copsvsninjas/Wicked/WickedBoard/WickedBoard.kicad_sch

## KiCad design WickedBoard/WickedBoard.kicad_sch (2024-12-09)

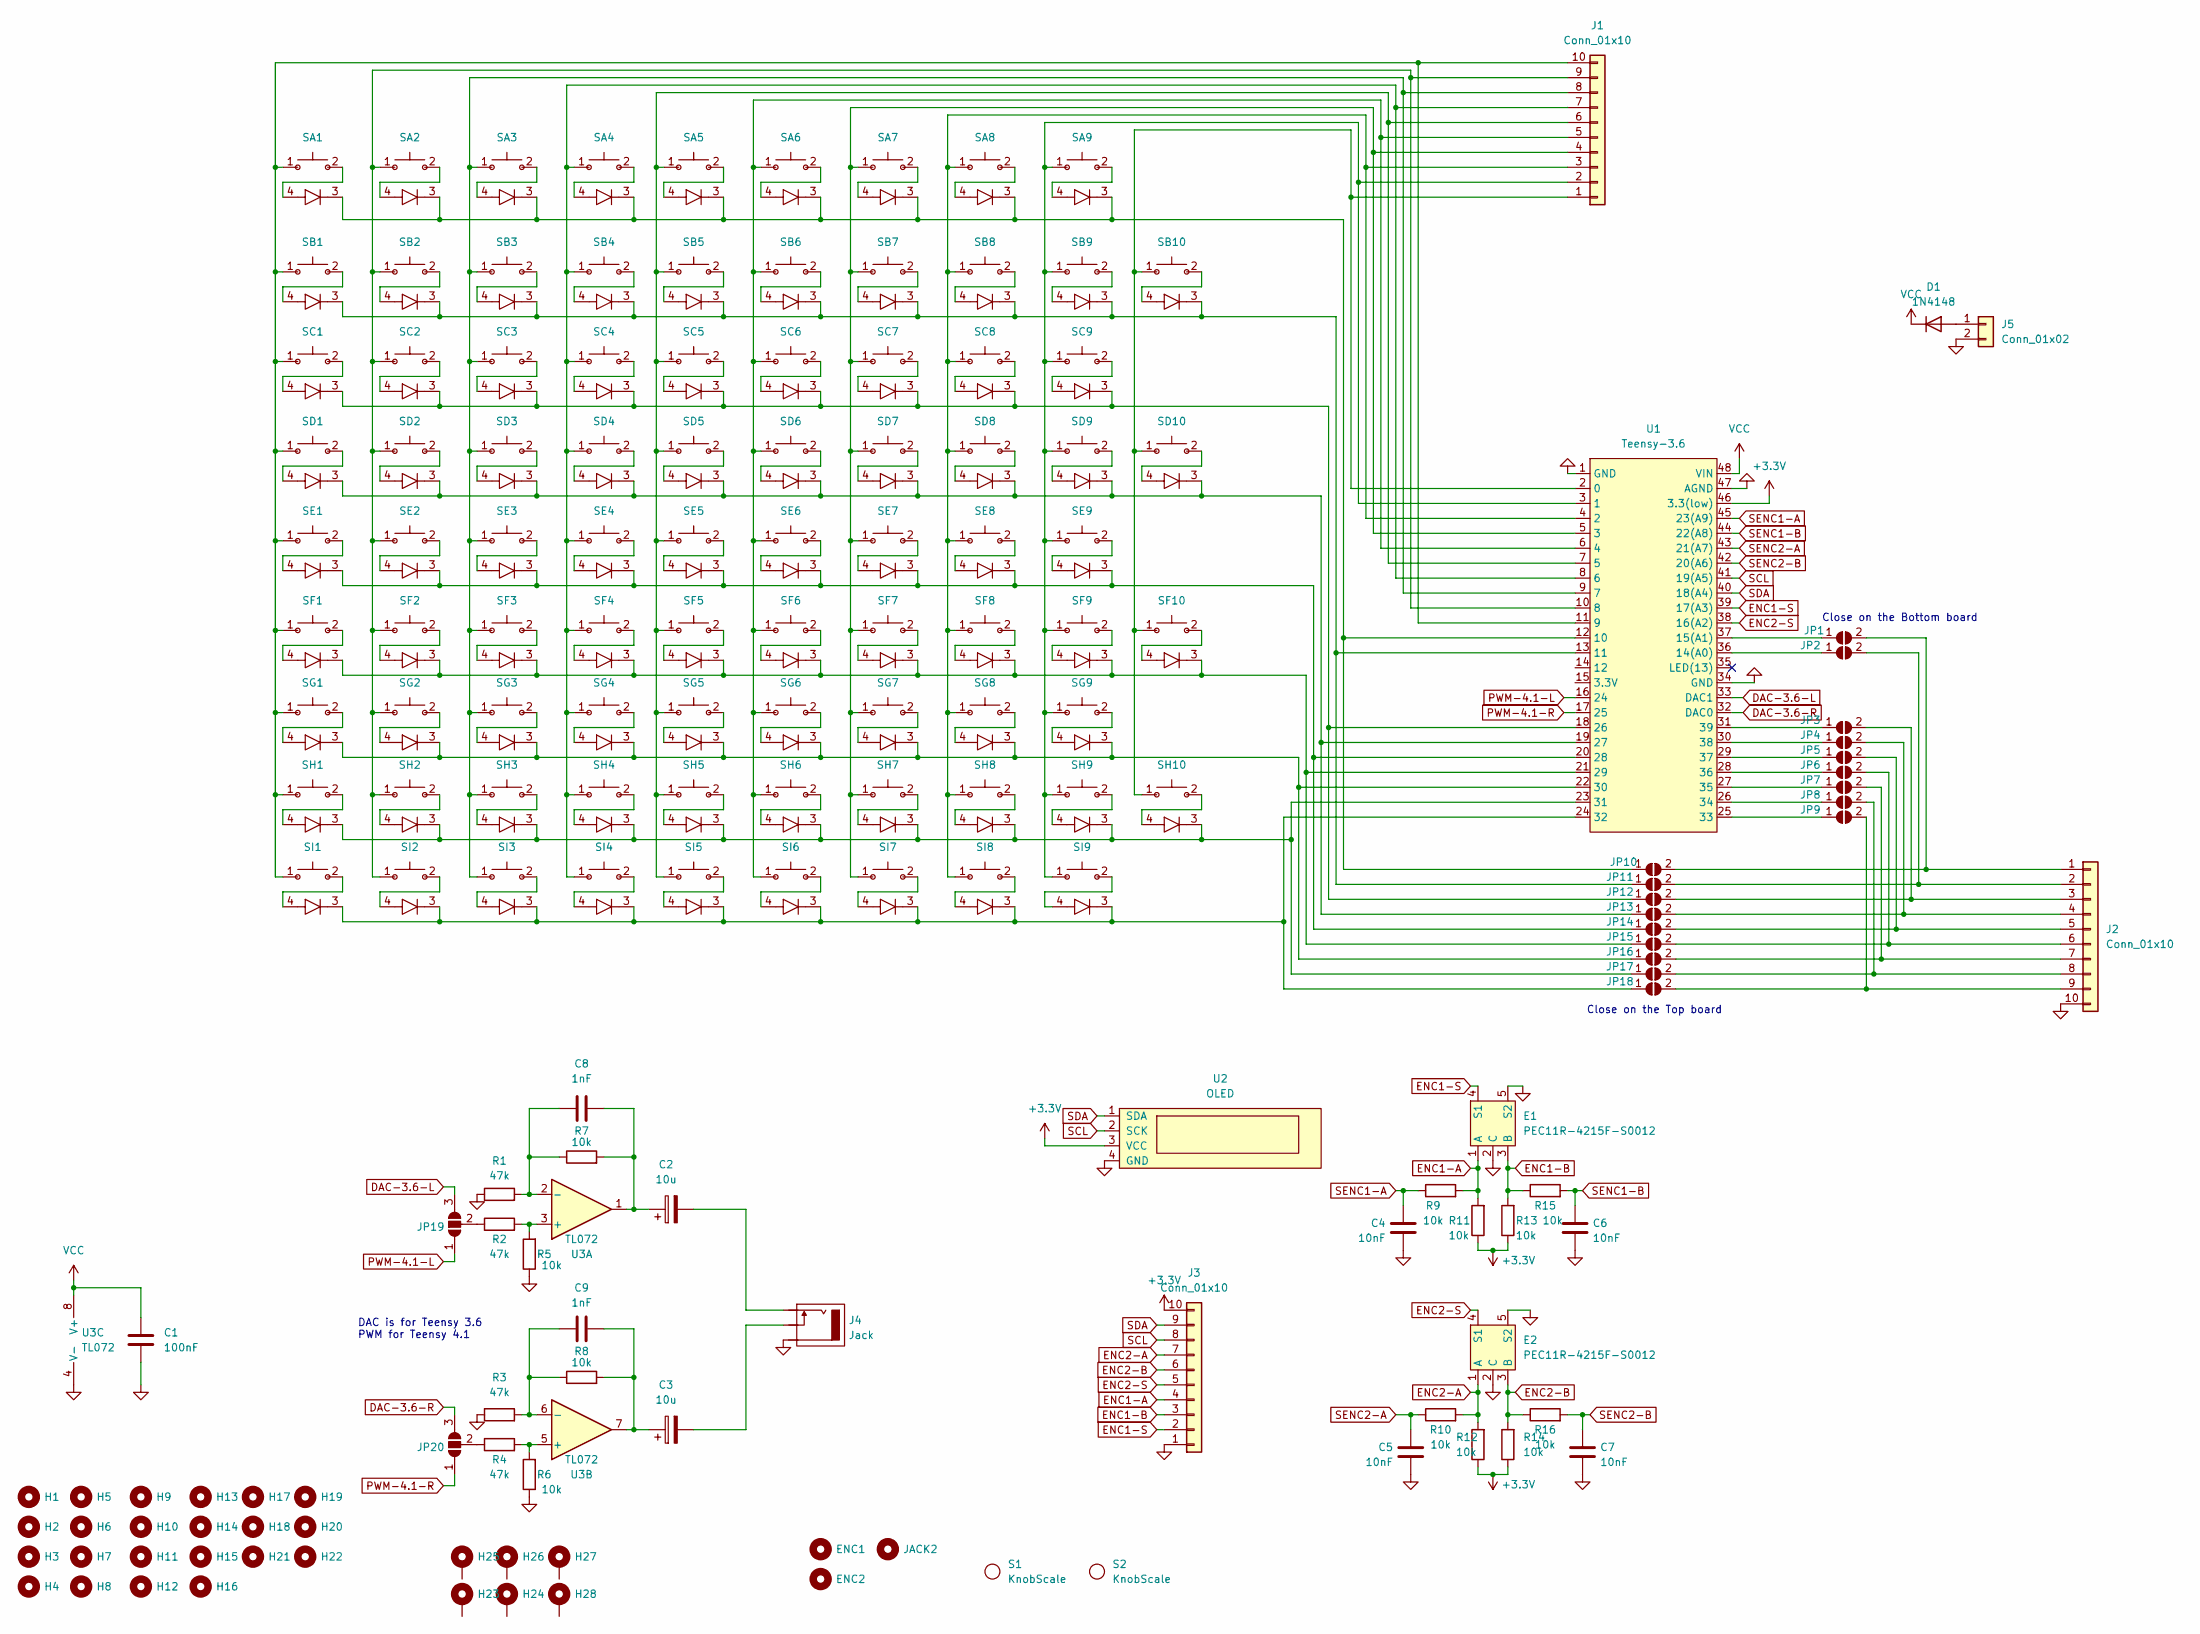
[picture p6: schematic WickedBoard.kicad_sch]

Parts:
C1: 100nF; C_Red_Thin
C2, C3: 10u; CP_Radial_D6.3mm_P2.50mm
C4, C5, C6, C7: 10nF; C_Red_Thin
C8, C9: 1nF; C_Red_Thin
D1: 1N4148; D_DO-35_SOD27_P7.62mm_Horizontal
E1, E2: PEC11R-4215F-S0012
ENC1, ENC2: MountingHole; KnobHole
H1, H2, H3, H4, H5, H6, H7, H8, H9, H10, H11, H12, H13, H14, H15, H16, H21, H22: MountingHole; M3-Simple
H17, H18, H19, H20: MountingHole; MountingHole_3.2mm_M3
H23, H24, H25, H26, H27, H28: MountingHole_Pad; MouseBite
J1, J2, J3: Conn_01x10; PinHeader_1x10_P2.54mm_Vertical
J4: Jack
J5: Conn_01x02; PinHeader_1x02_P2.54mm_Vertical
JACK2: MountingHole; KnobHole
JP1, JP2, JP3, JP4, JP5, JP6, JP7, JP8, JP9, JP10, JP11, JP12, JP13, JP14, JP15, JP16, JP17, JP18: SolderJumper_2_Open; SolderJumper-2_P1.3mm_Open_RoundedPad1.0x1.5mm
JP19, JP20: SolderJumper_3_Open; SolderJumper-3_P1.3mm_Open_RoundedPad1.0x1.5mm
R1, R2, R3, R4: 47k; Resistor
R5, R6, R7, R8, R9, R10, R11, R12, R13, R14, R15, R16: 10k; Resistor
S1, S2: KnobScale
SA1, SA2, SA3, SA4, SA5, SA6, SA7, SA8, SA9: CherryMXCustom
SB1, SB2, SB3, SB4, SB5, SB6, SB7, SB8, SB9, SB10: CherryMXCustom
SC1, SC2, SC3, SC4, SC5, SC6, SC7, SC8, SC9: CherryMXCustom
SD1, SD2, SD3, SD4, SD5, SD6, SD7, SD8, SD9, SD10: CherryMXCustom
SE1, SE2, SE3, SE4, SE5, SE6, SE7, SE8, SE9: CherryMXCustom
SF1, SF2, SF3, SF4, SF5, SF6, SF7, SF8, SF9, SF10: CherryMXCustom
SG1, SG2, SG3, SG4, SG5, SG6, SG7, SG8, SG9: CherryMXCustom
SH1, SH2, SH3, SH4, SH5, SH6, SH7, SH8, SH9, SH10: CherryMXCustom
SI1, SI2, SI3, SI4, SI5, SI6, SI7, SI8, SI9: CherryMXCustom
U1: Teensy-3.6; Teensy-3.6-THT
U2: OLED
U3: TL072; DIP-8_W7.62mm

Connections:
+3.3V: J3.10, R11.1, R12.1, R13.1, R14.1, U1.46 (3.3(low)), U2.3 (VCC)
DAC-3.6-L: JP19.3 (B), U1.33 (DAC1)
DAC-3.6-R: JP20.3 (B), U1.32 (DAC0)
ENC1-A: E1.1 (A), J3.4, R9.2, R11.2
ENC1-B: E1.3 (B), J3.3, R13.2, R15.1
ENC1-S: E1.4 (S1), J3.2, U1.39 (17(A3))
ENC2-A: E2.1 (A), J3.7, R10.2, R12.2
ENC2-B: E2.3 (B), J3.6, R14.2, R16.1
ENC2-S: E2.4 (S1), J3.5, U1.38 (16(A2))
GND: C1.2, C4.1, C5.1, C6.2, C7.2, E1.2 (C), E1.5 (S2), E2.2 (C), E2.5 (S2), J2.10, J3.1, J4.3, J5.2, R1.1, R3.1, R5.1, R6.1, U1.1 (GND), U1.34 (GND), U1.47 (AGND), U2.4 (GND), U3.4 (V-)
unnamed: C2.1, C8.1, R7.2, U3.1
unnamed: C2.2, J4.1
unnamed: C3.1, C9.1, R8.2, U3.7
unnamed: C3.2, J4.2
unnamed: C8.2, R1.2, R7.1, U3.2 (-)
unnamed: C9.2, R3.2, R8.1, U3.6 (-)
unnamed: D1.2 (A), J5.1
unnamed: J1.1, SB10.1, SD10.1, SF10.1, SH10.1, U1.2 (0)
unnamed: J1.2, SA9.1, SB9.1, SC9.1, SD9.1, SE9.1, SF9.1, SG9.1, SH9.1, SI9.1, U1.3 (1)
unnamed: J1.3, SA8.1, SB8.1, SC8.1, SD8.1, SE8.1, SF8.1, SG8.1, SH8.1, SI8.1, U1.4 (2)
unnamed: J1.4, SA7.1, SB7.1, SC7.1, SD7.1, SE7.1, SF7.1, SG7.1, SH7.1, SI7.1, U1.5 (3)
unnamed: J1.5, SA6.1, SB6.1, SC6.1, SD6.1, SE6.1, SF6.1, SG6.1, SH6.1, SI6.1, U1.6 (4)
unnamed: J1.6, SA5.1, SB5.1, SC5.1, SD5.1, SE5.1, SF5.1, SG5.1, SH5.1, SI5.1, U1.7 (5)
unnamed: J1.7, SA4.1, SB4.1, SC4.1, SD4.1, SE4.1, SF4.1, SG4.1, SH4.1, SI4.1, U1.8 (6)
unnamed: J1.8, SA3.1, SB3.1, SC3.1, SD3.1, SE3.1, SF3.1, SG3.1, SH3.1, SI3.1, U1.9 (7)
unnamed: J1.9, SA2.1, SB2.1, SC2.1, SD2.1, SE2.1, SF2.1, SG2.1, SH2.1, SI2.1, U1.10 (8)
unnamed: J1.10, SA1.1, SB1.1, SC1.1, SD1.1, SE1.1, SF1.1, SG1.1, SH1.1, SI1.1, U1.11 (9)
unnamed: J2.1, JP1.2 (B), JP10.2 (B)
unnamed: J2.2, JP2.2 (B), JP11.2 (B)
unnamed: J2.3, JP3.2 (B), JP12.2 (B)
unnamed: J2.4, JP4.2 (B), JP13.2 (B)
unnamed: J2.5, JP5.2 (B), JP14.2 (B)
unnamed: J2.6, JP6.2 (B), JP15.2 (B)
unnamed: J2.7, JP7.2 (B), JP16.2 (B)
unnamed: J2.8, JP8.2 (B), JP17.2 (B)
unnamed: J2.9, JP9.2 (B), JP18.2 (B)
unnamed: JP1.1 (A), U1.37 (15(A1))
unnamed: JP2.1 (A), U1.36 (14(A0))
unnamed: JP3.1 (A), U1.31 (39)
unnamed: JP4.1 (A), U1.30 (38)
unnamed: JP5.1 (A), U1.29 (37)
unnamed: JP6.1 (A), U1.28 (36)
unnamed: JP7.1 (A), U1.27 (35)
unnamed: JP8.1 (A), U1.26 (34)
unnamed: JP9.1 (A), U1.25 (33)
unnamed: JP10.1 (A), SA1.3, SA2.3, SA3.3, SA4.3, SA5.3, SA6.3, SA7.3, SA8.3, SA9.3, U1.12 (10)
unnamed: JP11.1 (A), SB1.3, SB2.3, SB3.3, SB4.3, SB5.3, SB6.3, SB7.3, SB8.3, SB9.3, SB10.3, U1.13 (11)
unnamed: JP12.1 (A), SC1.3, SC2.3, SC3.3, SC4.3, SC5.3, SC6.3, SC7.3, SC8.3, SC9.3, U1.18 (26)
unnamed: JP13.1 (A), SD1.3, SD2.3, SD3.3, SD4.3, SD5.3, SD6.3, SD7.3, SD8.3, SD9.3, SD10.3, U1.19 (27)
unnamed: JP14.1 (A), SE1.3, SE2.3, SE3.3, SE4.3, SE5.3, SE6.3, SE7.3, SE8.3, SE9.3, U1.20 (28)
unnamed: JP15.1 (A), SF1.3, SF2.3, SF3.3, SF4.3, SF5.3, SF6.3, SF7.3, SF8.3, SF9.3, SF10.3, U1.21 (29)
unnamed: JP16.1 (A), SG1.3, SG2.3, SG3.3, SG4.3, SG5.3, SG6.3, SG7.3, SG8.3, SG9.3, U1.22 (30)
unnamed: JP17.1 (A), SH1.3, SH2.3, SH3.3, SH4.3, SH5.3, SH6.3, SH7.3, SH8.3, SH9.3, SH10.3, U1.23 (31)
unnamed: JP18.1 (A), SI1.3, SI2.3, SI3.3, SI4.3, SI5.3, SI6.3, SI7.3, SI8.3, SI9.3, U1.24 (32)
unnamed: JP19.2 (C), R2.1
unnamed: JP20.2 (C), R4.1
unnamed: R2.2, R5.2, U3.3 (+)
unnamed: R4.2, R6.2, U3.5 (+)
unnamed: SA1.2, SA1.4
unnamed: SA2.2, SA2.4
unnamed: SA3.2, SA3.4
unnamed: SA4.2, SA4.4
unnamed: SA5.2, SA5.4
unnamed: SA6.2, SA6.4
unnamed: SA7.2, SA7.4
unnamed: SA8.2, SA8.4
unnamed: SA9.2, SA9.4
unnamed: SB1.2, SB1.4
unnamed: SB2.2, SB2.4
unnamed: SB3.2, SB3.4
unnamed: SB4.2, SB4.4
unnamed: SB5.2, SB5.4
unnamed: SB6.2, SB6.4
unnamed: SB7.2, SB7.4
unnamed: SB8.2, SB8.4
unnamed: SB9.2, SB9.4
unnamed: SB10.2, SB10.4
unnamed: SC1.2, SC1.4
unnamed: SC2.2, SC2.4
unnamed: SC3.2, SC3.4
unnamed: SC4.2, SC4.4
unnamed: SC5.2, SC5.4
unnamed: SC6.2, SC6.4
unnamed: SC7.2, SC7.4
unnamed: SC8.2, SC8.4
unnamed: SC9.2, SC9.4
unnamed: SD1.2, SD1.4
unnamed: SD2.2, SD2.4
unnamed: SD3.2, SD3.4
unnamed: SD4.2, SD4.4
unnamed: SD5.2, SD5.4
unnamed: SD6.2, SD6.4
unnamed: SD7.2, SD7.4
unnamed: SD8.2, SD8.4
unnamed: SD9.2, SD9.4
unnamed: SD10.2, SD10.4
unnamed: SE1.2, SE1.4
unnamed: SE2.2, SE2.4
unnamed: SE3.2, SE3.4
unnamed: SE4.2, SE4.4
unnamed: SE5.2, SE5.4
unnamed: SE6.2, SE6.4
unnamed: SE7.2, SE7.4
unnamed: SE8.2, SE8.4
unnamed: SE9.2, SE9.4
unnamed: SF1.2, SF1.4
unnamed: SF2.2, SF2.4
unnamed: SF3.2, SF3.4
unnamed: SF4.2, SF4.4
unnamed: SF5.2, SF5.4
unnamed: SF6.2, SF6.4
unnamed: SF7.2, SF7.4
unnamed: SF8.2, SF8.4
unnamed: SF9.2, SF9.4
unnamed: SF10.2, SF10.4
unnamed: SG1.2, SG1.4
unnamed: SG2.2, SG2.4
unnamed: SG3.2, SG3.4
unnamed: SG4.2, SG4.4
unnamed: SG5.2, SG5.4
unnamed: SG6.2, SG6.4
unnamed: SG7.2, SG7.4
unnamed: SG8.2, SG8.4
unnamed: SG9.2, SG9.4
unnamed: SH1.2, SH1.4
unnamed: SH2.2, SH2.4
unnamed: SH3.2, SH3.4
unnamed: SH4.2, SH4.4
unnamed: SH5.2, SH5.4
unnamed: SH6.2, SH6.4
unnamed: SH7.2, SH7.4
unnamed: SH8.2, SH8.4
unnamed: SH9.2, SH9.4
unnamed: SH10.2, SH10.4
unnamed: SI1.2, SI1.4
unnamed: SI2.2, SI2.4
unnamed: SI3.2, SI3.4
unnamed: SI4.2, SI4.4
unnamed: SI5.2, SI5.4
unnamed: SI6.2, SI6.4
unnamed: SI7.2, SI7.4
unnamed: SI8.2, SI8.4
unnamed: SI9.2, SI9.4
PWM-4.1-L: JP19.1 (A), U1.16 (24)
PWM-4.1-R: JP20.1 (A), U1.17 (25)
SCL: J3.8, U1.41 (19(A5)), U2.2 (SCK)
SDA: J3.9, U1.40 (18(A4)), U2.1 (SDA)
SENC1-A: C4.2, R9.1, U1.45 (23(A9))
SENC1-B: C6.1, R15.2, U1.44 (22(A8))
SENC2-A: C5.2, R10.1, U1.43 (21(A7))
SENC2-B: C7.1, R16.2, U1.42 (20(A6))
VCC: C1.1, D1.1 (K), U1.48 (VIN), U3.8 (V+)

Notes on the sheet:
Close on the Bottom board
DAC is for Teensy 3.6 PWM for Teensy 4.1
Close on the Top board
